vega-d/qidi_mods/qidi 3d models/Toolhead/Typ-C Kabel Unterlage.STEP

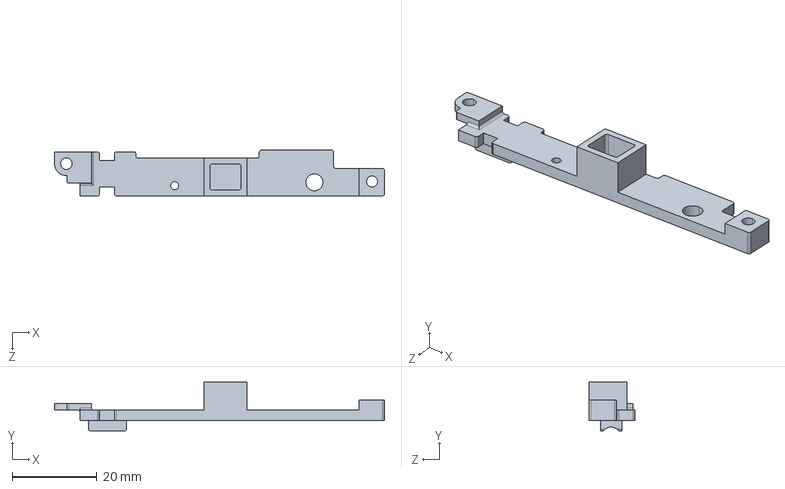
[picture p15: CAD file, 2024-07-16]
qidi 3d models/Toolhead/Typ-C Kabel Unterlage.STEP
77.7 x 11.5 x 10.8 mm
