vega-d/qidi_mods/qidi 3d models/Toolhead/Druckkopfabdeckung hinten.STEP

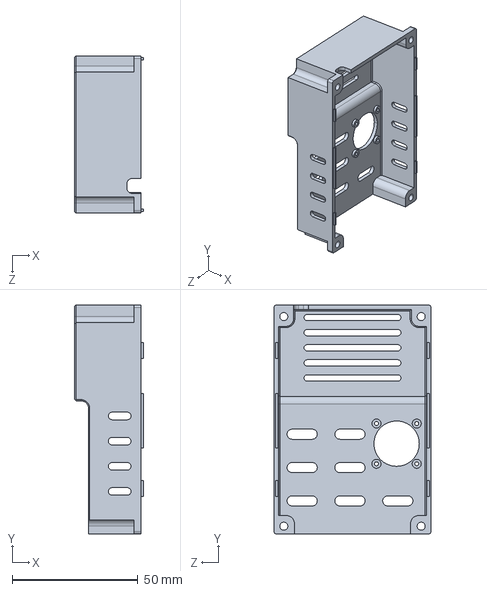
[picture p16: CAD file, 2024-07-16]
qidi 3d models/Toolhead/Druckkopfabdeckung hinten.STEP
27.3 x 91.0 x 62.4 mm
